ItzzInfinity/FM-Radio-Using-ESP-12E-and-RDA5807M/Demo/img2.jpeg

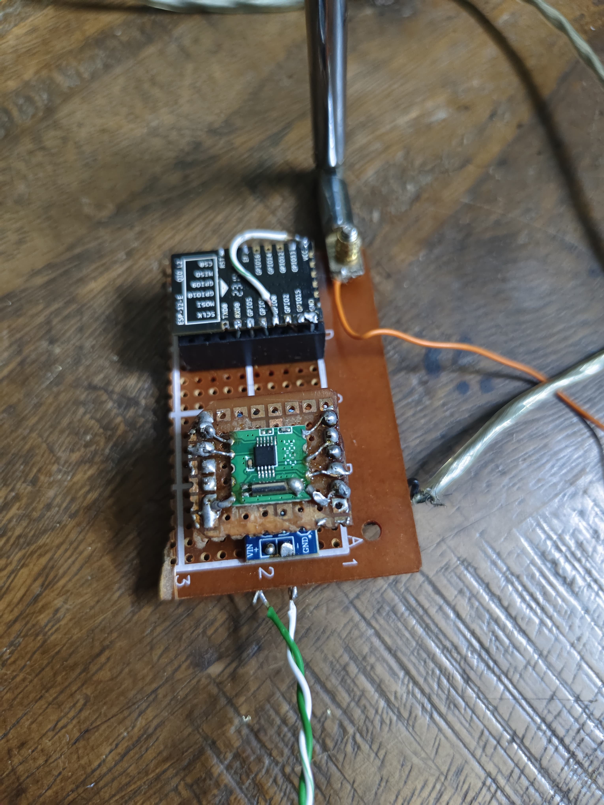
Demo/img2.jpeg
