ItzzInfinity/FM-Radio-Using-ESP-12E-and-RDA5807M/Demo/img3.jpeg

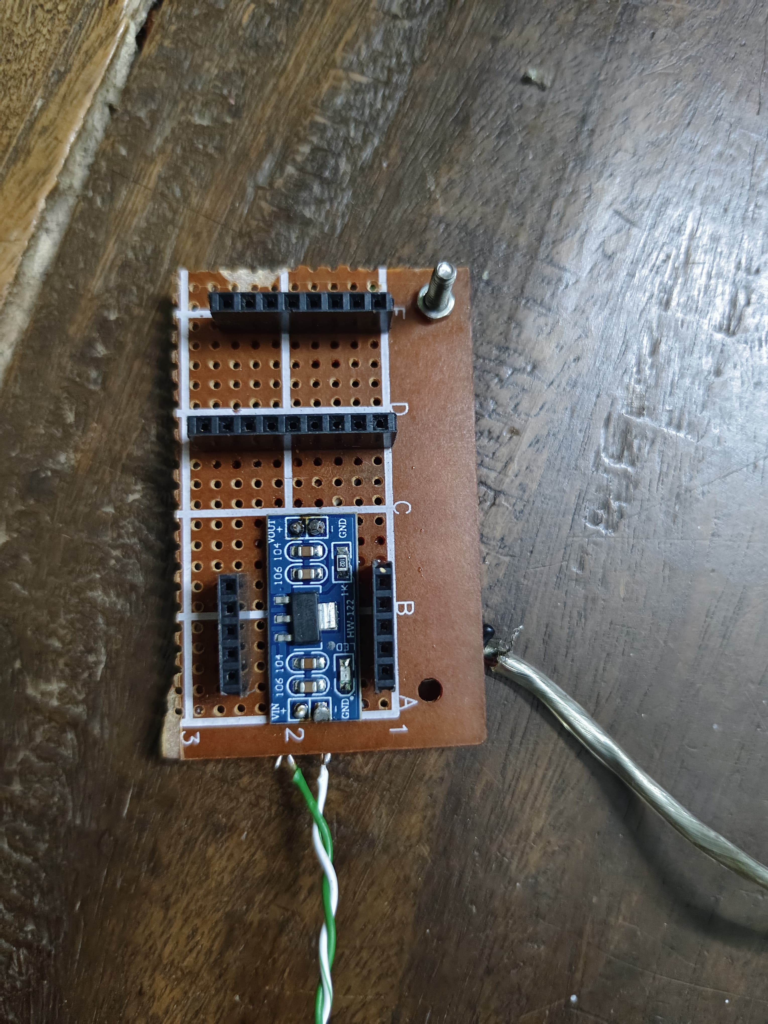
Demo/img3.jpeg
