ItzzInfinity/FM-Radio-Using-ESP-12E-and-RDA5807M/Demo/img4.jpeg

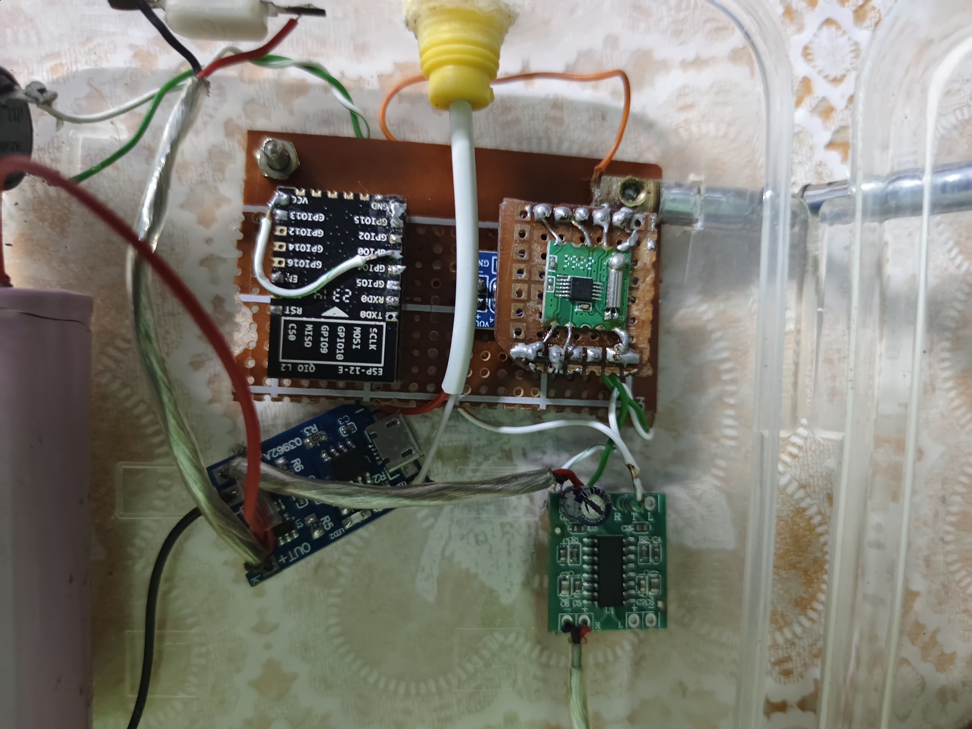
Demo/img4.jpeg
